ctorres8/Cartel-Led/Proyecto_STM32/Core/Src/dht11.c

/*
 * dht11.c
 *
 *  Created on: 17 oct. 2022
 *      Author: Jonathan
 */
/* USER CODE BEGIN 0 */
#include "main.h"
//#include "dht11.h"

#define DHT11_PORT GPIOB
#define DHT11_PIN GPIO_PIN_1

uint32_t pMillis, cMillis;

extern TIM_HandleTypeDef htim3;

void microDelay (uint16_t delay)
{
  __HAL_TIM_SET_COUNTER(&htim3, 0);

  while (__HAL_TIM_GET_COUNTER(&htim3)< delay);

}

uint8_t DHT11_Start (void)
{
  uint8_t Response = 0;
  GPIO_InitTypeDef GPIO_InitStructPrivate = {0};
  GPIO_InitStructPrivate.Pin = DHT11_PIN;
  GPIO_InitStructPrivate.Mode = GPIO_MODE_OUTPUT_PP;
  GPIO_InitStructPrivate.Speed = GPIO_SPEED_FREQ_LOW;
  GPIO_InitStructPrivate.Pull = GPIO_NOPULL;
  HAL_GPIO_Init(DHT11_PORT, &GPIO_InitStructPrivate); // set the pin as output
  HAL_GPIO_WritePin (DHT11_PORT, DHT11_PIN, 0);   // pull the pin low
  HAL_Delay(20);   // wait for 20ms
  HAL_GPIO_WritePin (DHT11_PORT, DHT11_PIN, 1);   // pull the pin high
  microDelay (30);   // wait for 30us
  GPIO_InitStructPrivate.Mode = GPIO_MODE_INPUT;
  GPIO_InitStructPrivate.Pull = GPIO_PULLUP;
  HAL_GPIO_Init(DHT11_PORT, &GPIO_InitStructPrivate); // set the pin as input
  microDelay (40);
  if (!(HAL_GPIO_ReadPin (DHT11_PORT, DHT11_PIN)))
  {
    microDelay (80);
    if ((HAL_GPIO_ReadPin (DHT11_PORT, DHT11_PIN))) Response = 1;
  }
  pMillis = HAL_GetTick();
  cMillis = HAL_GetTick();
  while ((HAL_GPIO_ReadPin (DHT11_PORT, DHT11_PIN)) && pMillis + 2 > cMillis)
  {
    cMillis = HAL_GetTick();
  }
  return Response;
}

uint8_t DHT11_Read (void)
{
  uint8_t a=0,b=0;
  for (a=0;a<8;a++)
  {
    pMillis = HAL_GetTick();
    cMillis = HAL_GetTick();
    while (!(HAL_GPIO_ReadPin (DHT11_PORT, DHT11_PIN)) && pMillis + 2 > cMillis)
    {  // wait for the pin to go high
      cMillis = HAL_GetTick();
    }
    microDelay (40);   // wait for 40 us
    if (!(HAL_GPIO_ReadPin (DHT11_PORT, DHT11_PIN)))   // if the pin is low
      b&= ~(1<<(7-a));
    else
      b|= (1<<(7-a));
    pMillis = HAL_GetTick();
    cMillis = HAL_GetTick();
    while ((HAL_GPIO_ReadPin (DHT11_PORT, DHT11_PIN)) && pMillis + 2 > cMillis)
    {  // wait for the pin to go low
      cMillis = HAL_GetTick();
    }
  }
  return b;
}
/* USER CODE END 0 */
/*
void tarea_DHT11(void)
{
	uint8_t RHI, RHD, TCI, TCD, SUM;
	uint8_t tCelsius = 0;

	while(1)
	{
		if(DHT11_Start())
		{
			 //RHI = DHT11_Read(); // Relative humidity integral
			 //RHD = DHT11_Read(); // Relative humidity decimal
			 TCI = DHT11_Read(); // Celsius integral
			 //TCD = DHT11_Read(); // Celsius decimal
			 //SUM = DHT11_Read(); // Check sum

			 //if (RHI + RHD + TCI + TCD == SUM)
			 //{
				 tCelsius = TCI;//(float)TCI + (float)(TCD/10.0);
			 //}
			vTaskDelay(5000);
		}

	}

}
*/
